sneakylizard123-4/FTDIboard/images/V1/closeup2.png

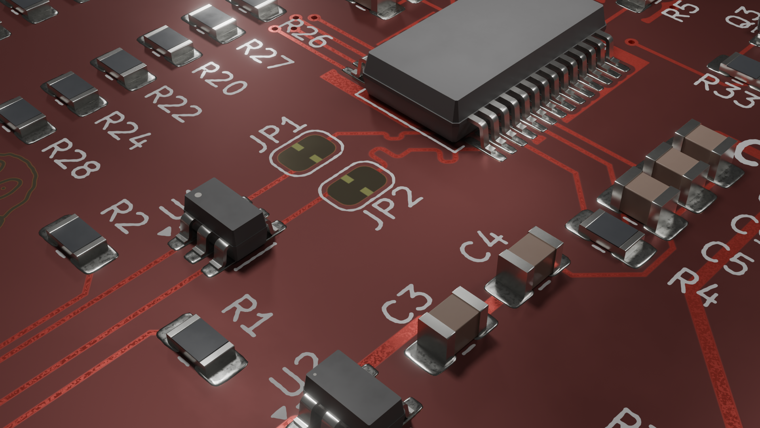
images/V1/closeup2.png
