sneakylizard123-4/FTDIboard/images/V1/paste_2.jpg

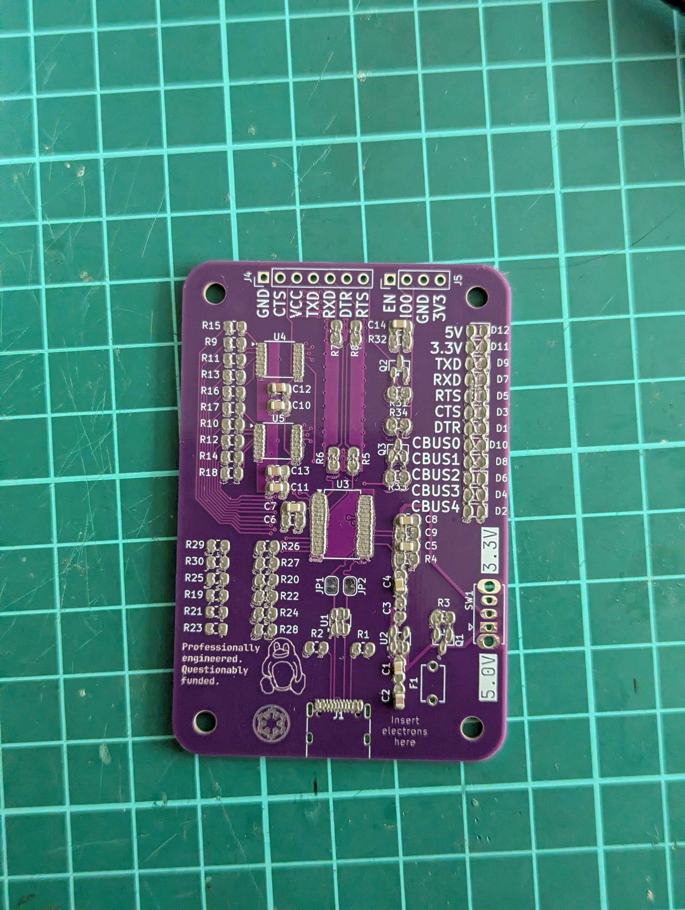
images/V1/paste_2.jpg
