sneakylizard123-4/FTDIboard/images/V1/paste_3.jpg

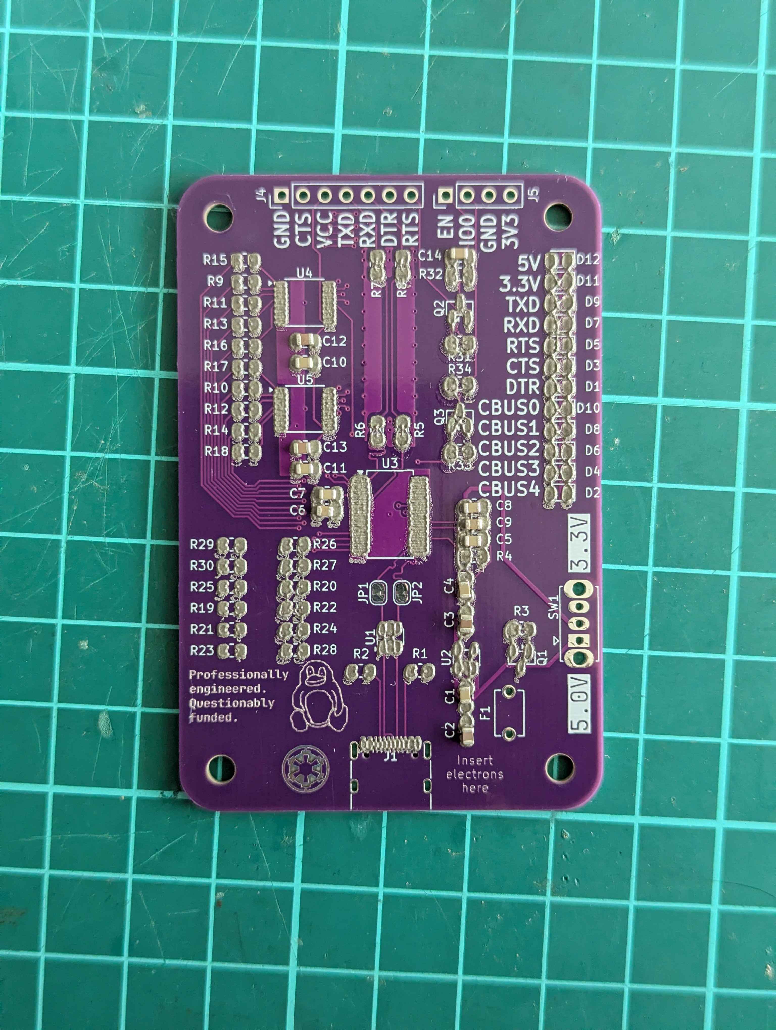
images/V1/paste_3.jpg
