sneakylizard123-4/FTDIboard/images/V1/paste_4.jpg

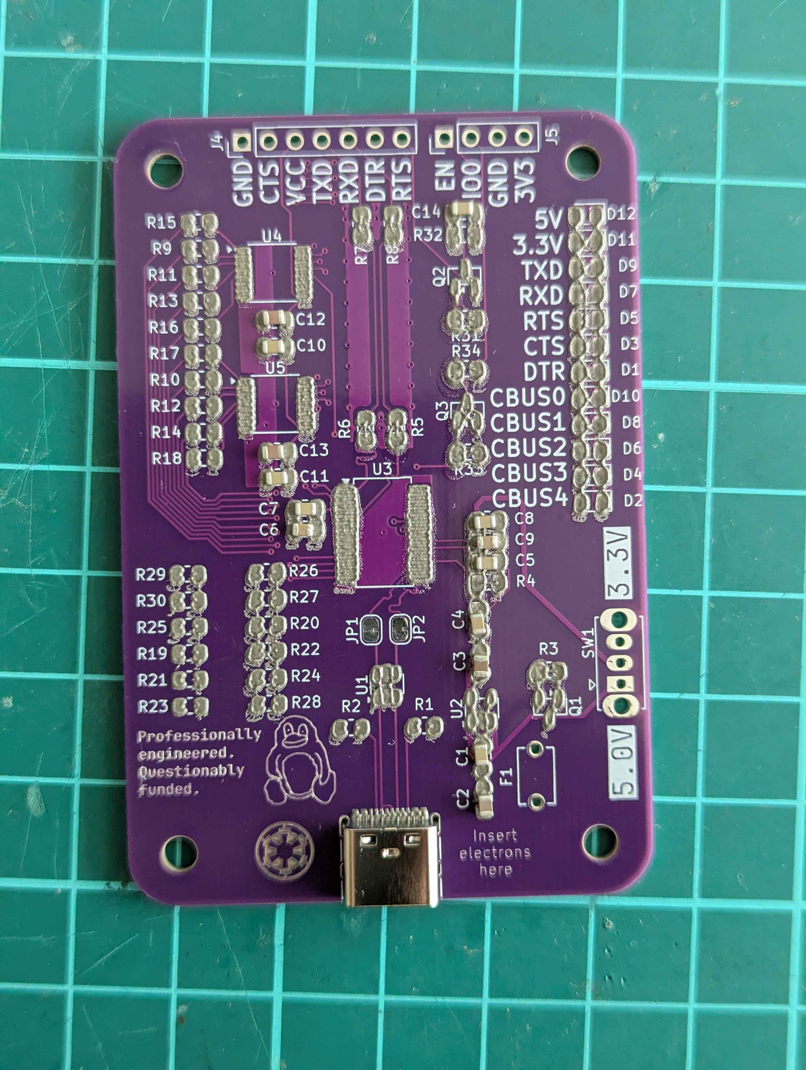
images/V1/paste_4.jpg
