sneakylizard123-4/FTDIboard/images/V1/paste_7.jpg

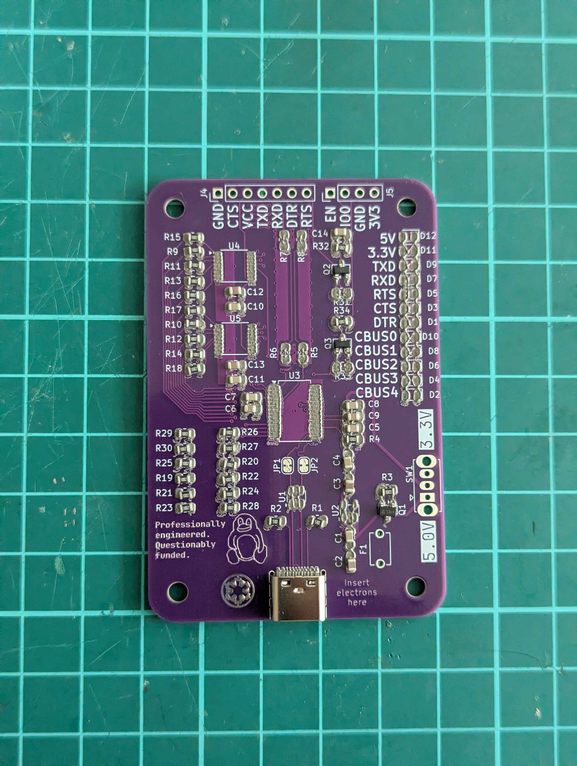
images/V1/paste_7.jpg
