sneakylizard123-4/FTDIboard/images/V1/paste_8.jpg

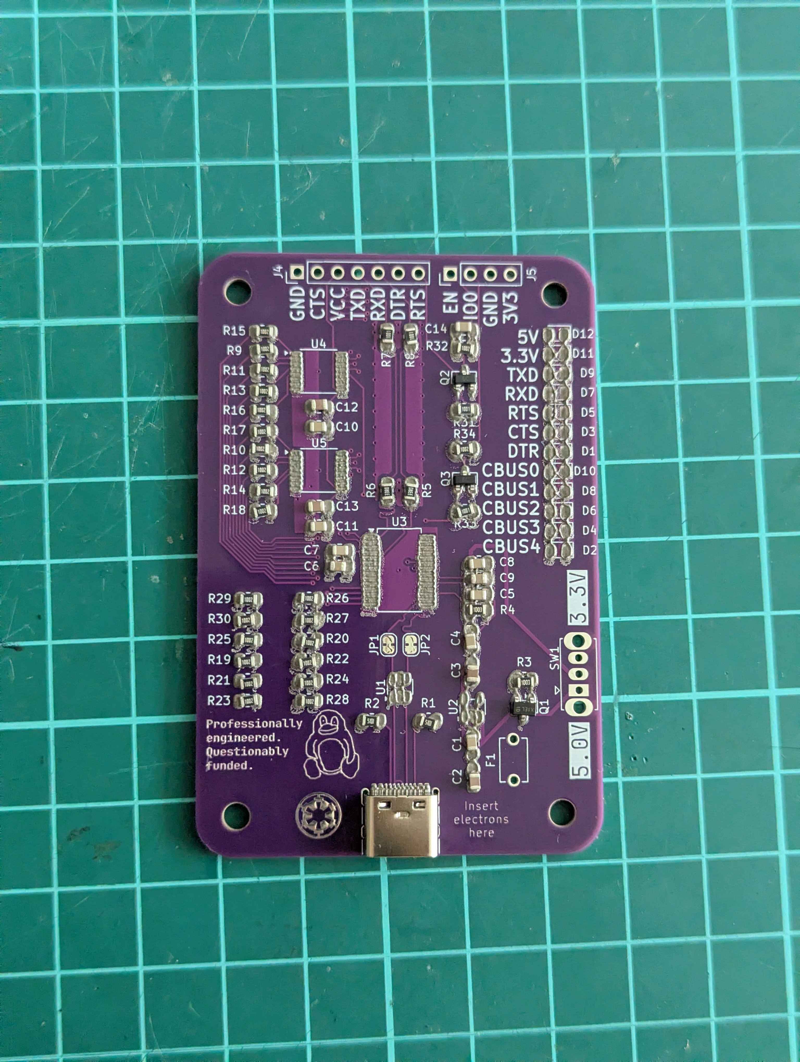
images/V1/paste_8.jpg
