sneakylizard123-4/FTDIboard/images/V1/paste_9.jpg

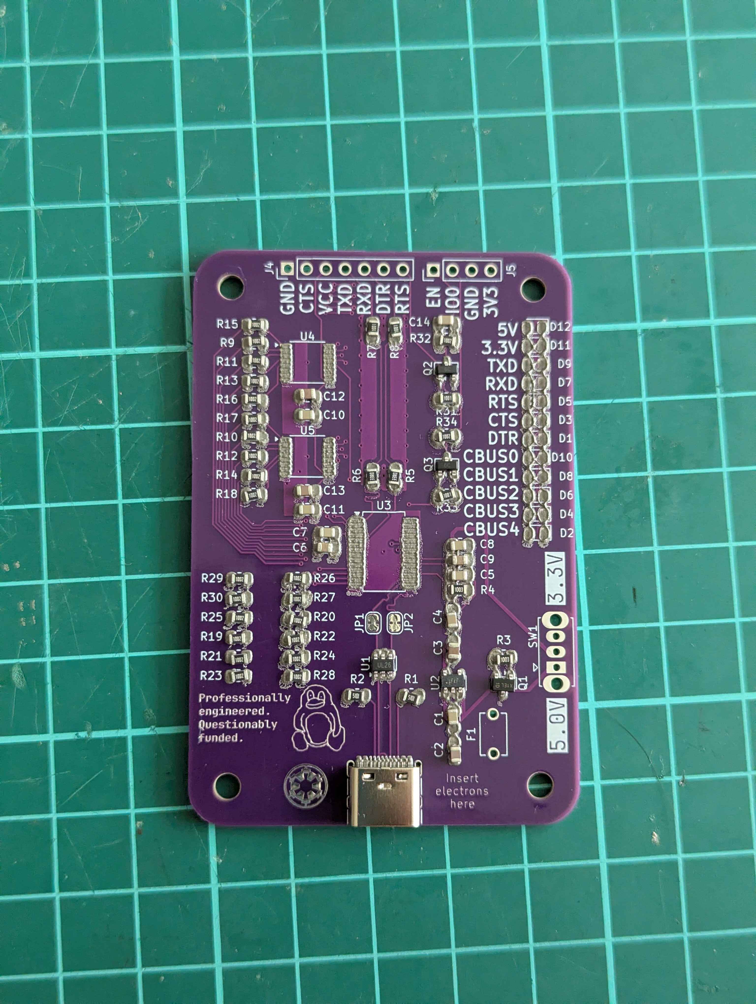
images/V1/paste_9.jpg
