sneakylizard123-4/FTDIboard/images/V1/paste_11.jpg

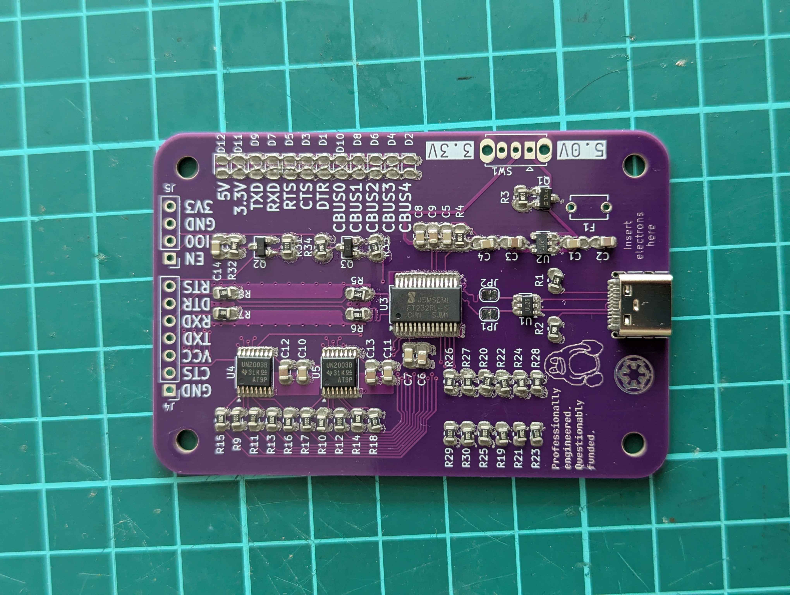
images/V1/paste_11.jpg
