sneakylizard123-4/FTDIboard/proof/V1/image/IMG_20260908_173817_623.jpg

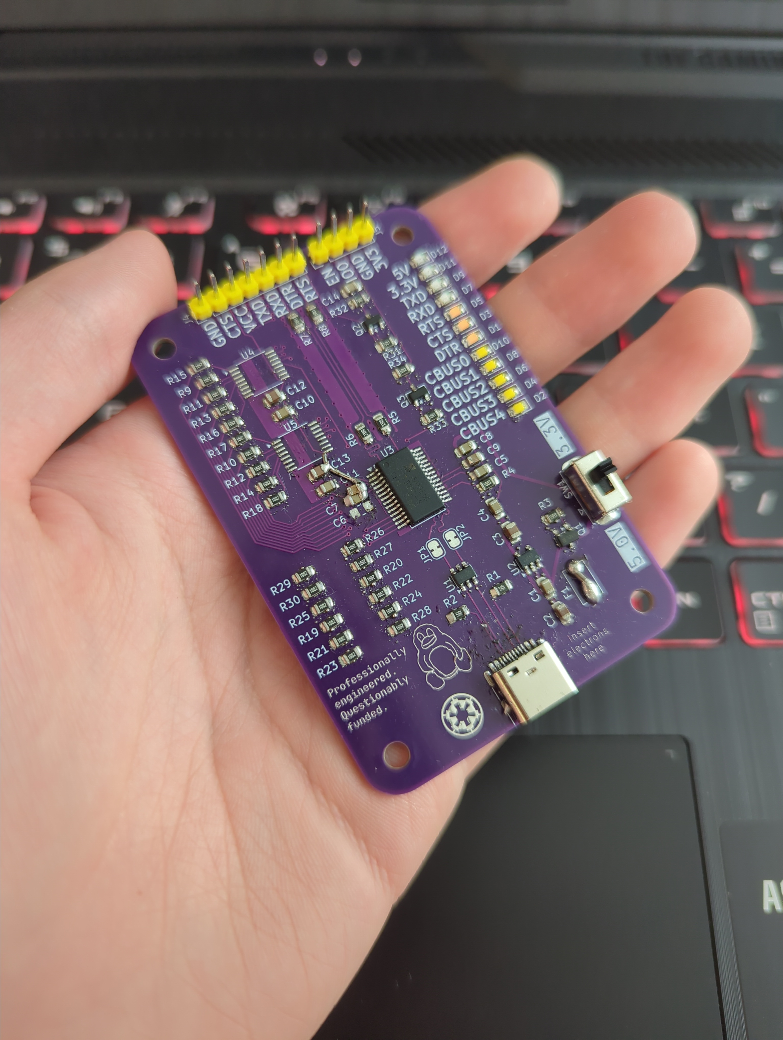
proof/V1/image/IMG_20260908_173817_623.jpg
